SuperHouse/RACK32/Images/P1020121.JPG

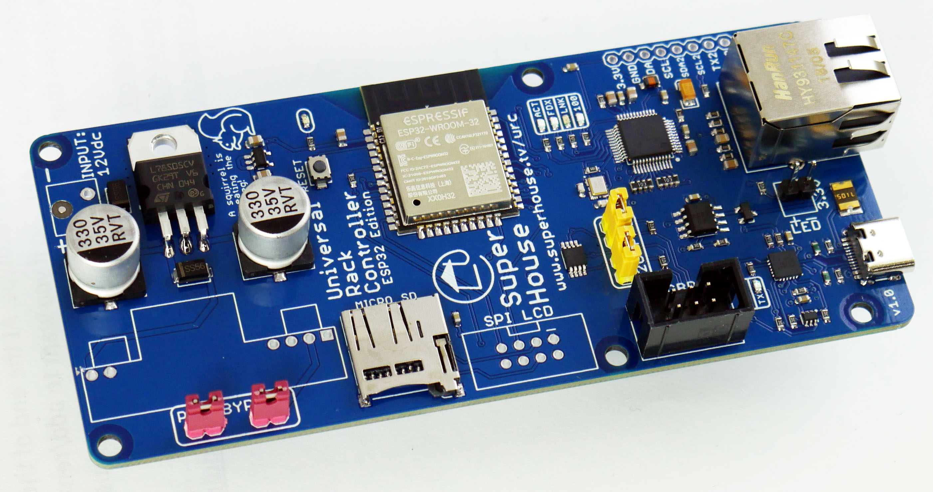
Images/P1020121.JPG
