SuperHouse/RACK32/Images/P1020122.JPG

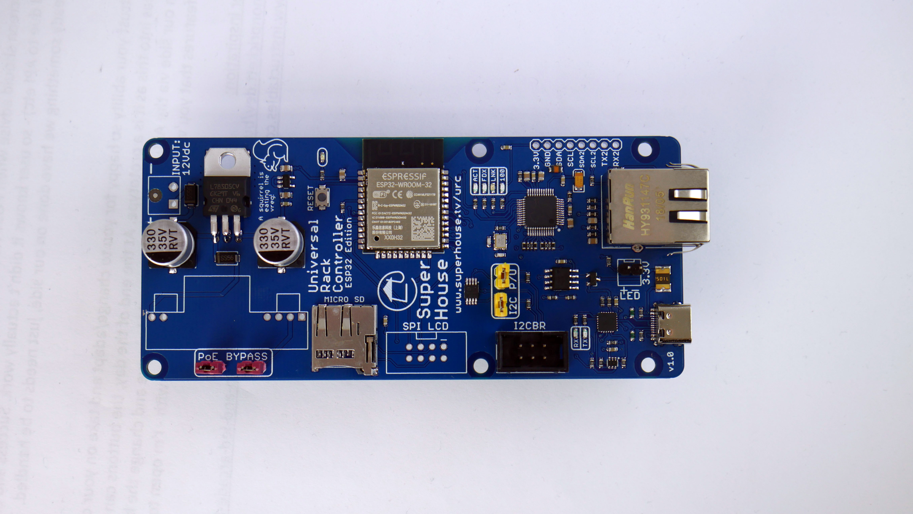
Images/P1020122.JPG
