SuperHouse/RACK32/Images/P1020123.JPG

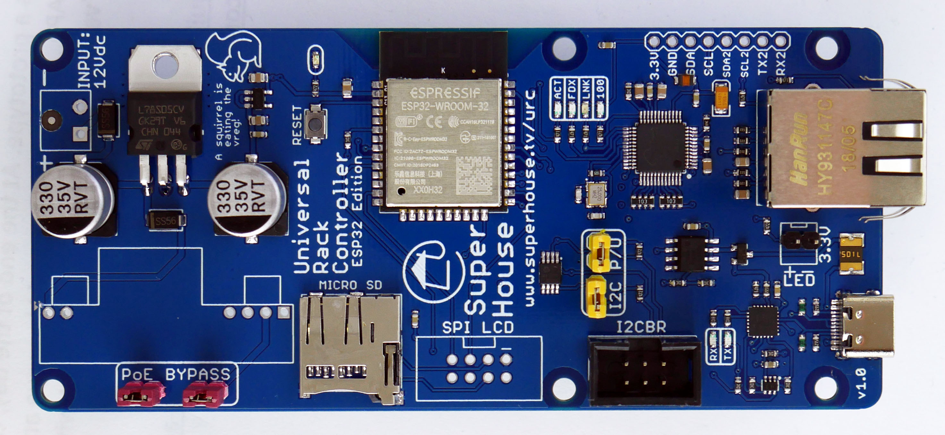
Images/P1020123.JPG
