SuperHouse/RACK32/Images/P1020124.JPG

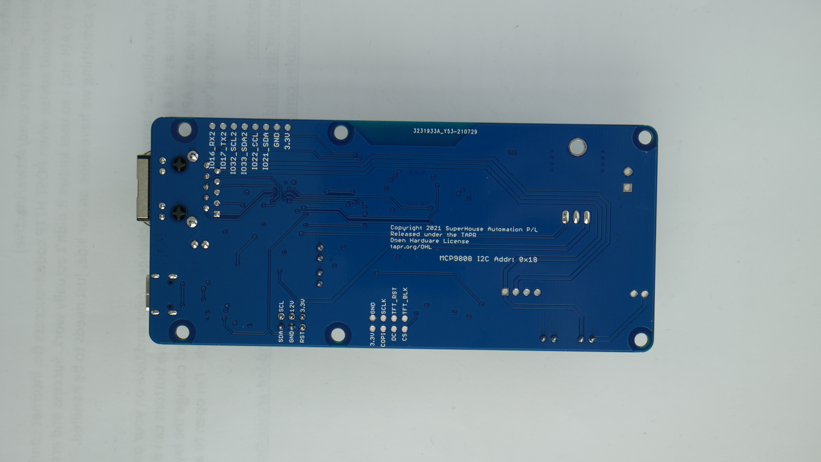
Images/P1020124.JPG
