SuperHouse/RACK32/Images/P1020125.JPG

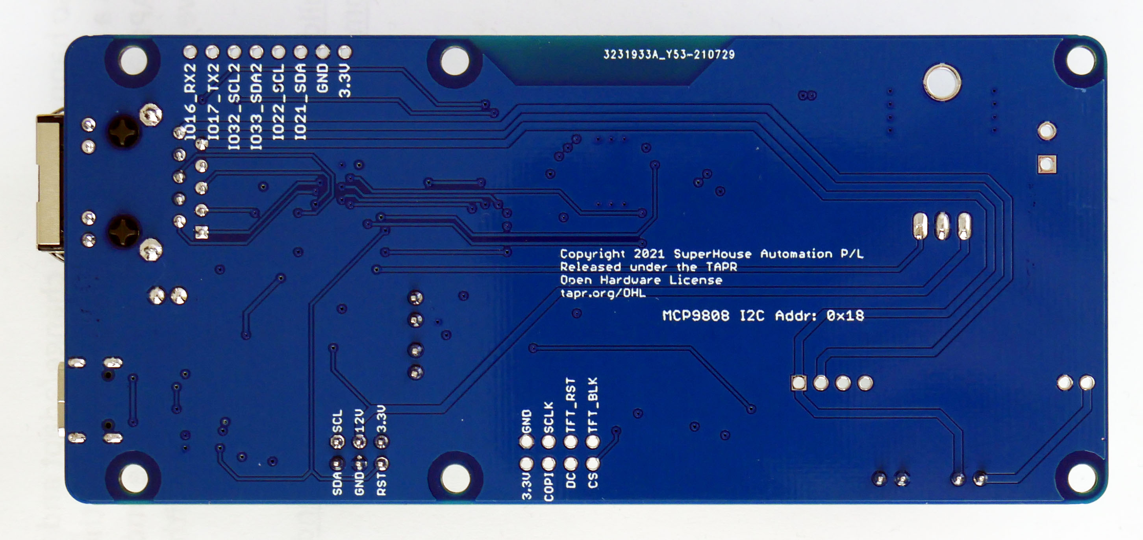
Images/P1020125.JPG
